4dennis/Automated-Fluid-Dispenser/AFD_SOLIDWORKS/054_BearingOuterRing_NOPRINT_N1.SLDPRT

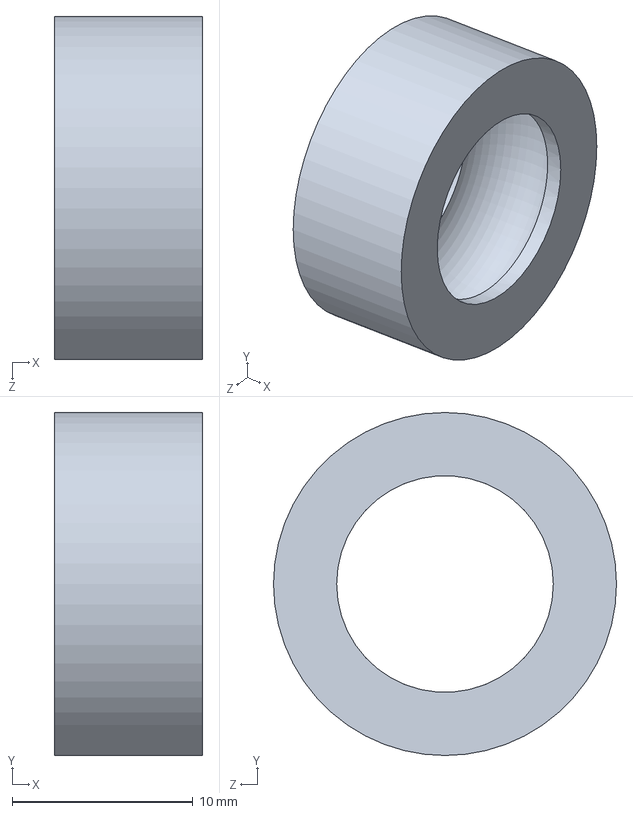
[picture p20: CAD file, 2023-12-04]
AFD_SOLIDWORKS/054_BearingOuterRing_NOPRINT_N1.SLDPRT
8.20 x 19.0 x 19.0 mm
