4dennis/Automated-Fluid-Dispenser/AFD_SOLIDWORKS/054_Motorshield_NOPRINT_N1.SLDPRT

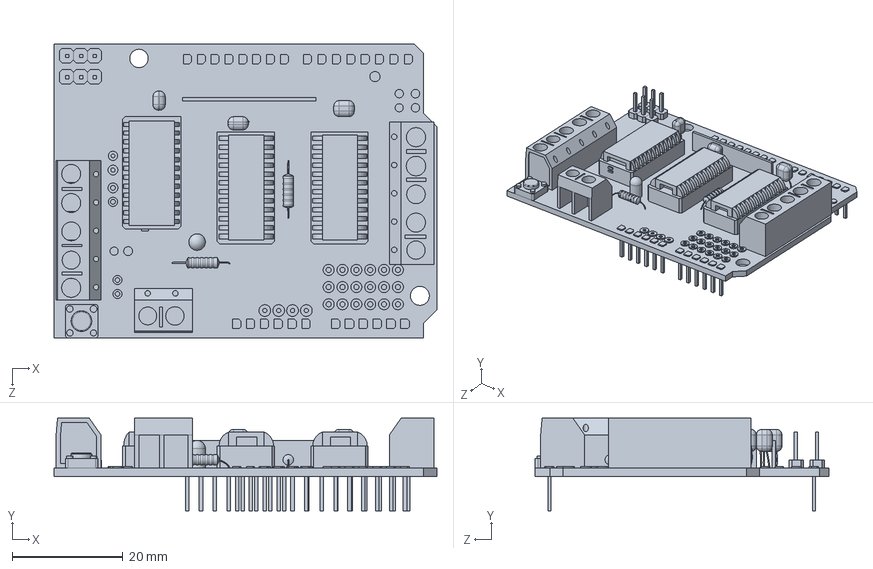
[picture p21: CAD file, 2023-12-04]
AFD_SOLIDWORKS/054_Motorshield_NOPRINT_N1.SLDPRT
69.1 x 16.7 x 53.1 mm
