4dennis/Automated-Fluid-Dispenser/AFD_SOLIDWORKS/054_Pump_NOPRINT_N1.SLDPRT

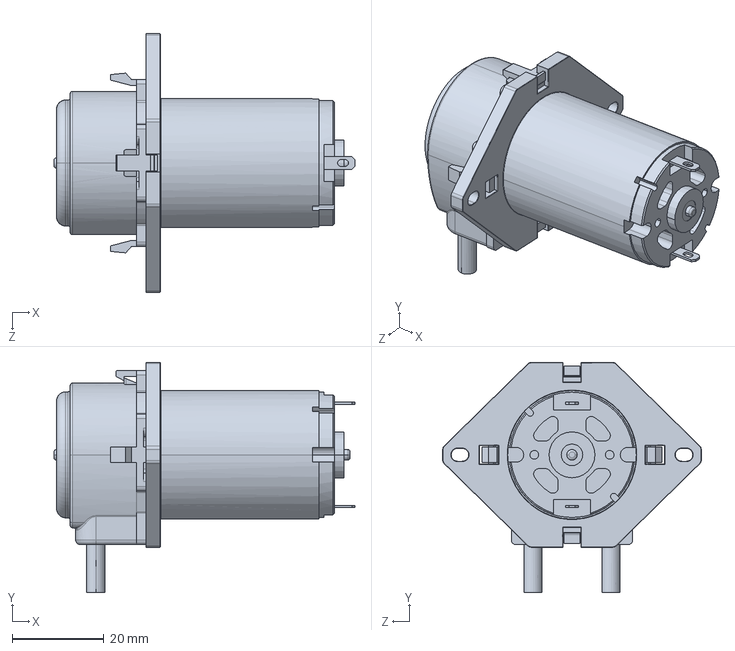
[picture p22: CAD file, 2023-12-04]
AFD_SOLIDWORKS/054_Pump_NOPRINT_N1.SLDPRT
65.5 x 50.1 x 56.3 mm
