4dennis/Automated-Fluid-Dispenser/AFD_SOLIDWORKS/054_Shaft_NOPRINT_N4.SLDPRT

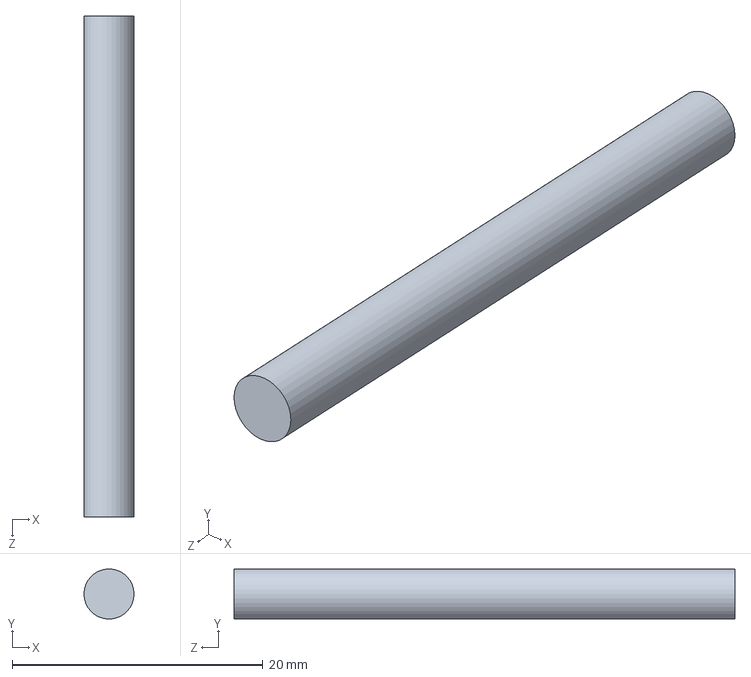
[picture p23: CAD file, 2023-12-04]
AFD_SOLIDWORKS/054_Shaft_NOPRINT_N4.SLDPRT
4.00 x 3.98 x 40.0 mm
