4dennis/Automated-Fluid-Dispenser/AFD_SOLIDWORKS/054_topofmast_AC_N1.SLDPRT

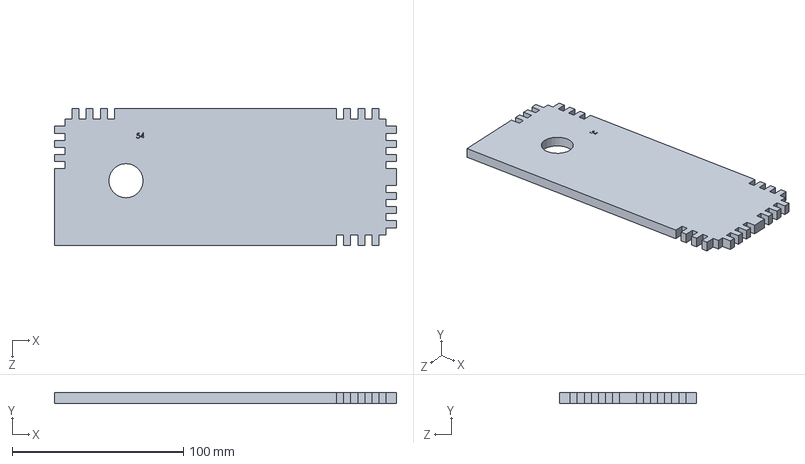
[picture p24: CAD file, 2023-12-04]
AFD_SOLIDWORKS/054_topofmast_AC_N1.SLDPRT
200.0 x 6.20 x 80.0 mm
