4dennis/Automated-Fluid-Dispenser/AFD_SOLIDWORKS/Servo_SG90 - Updated.SLDPRT

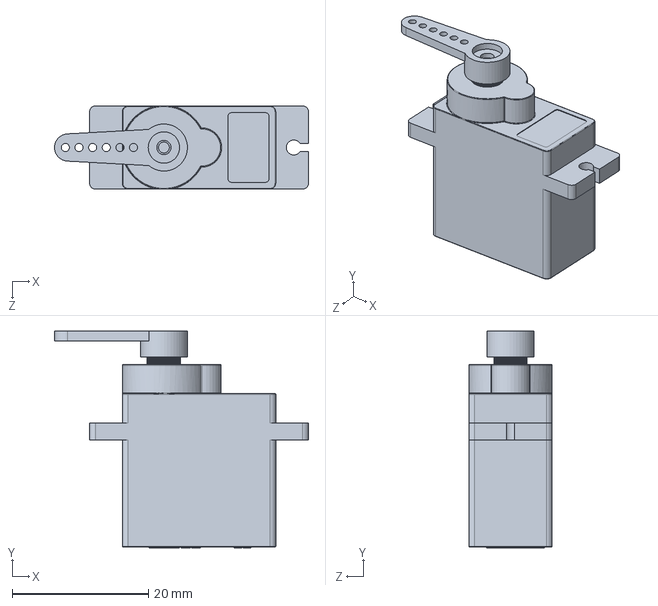
[picture p25: CAD file, 2023-12-04]
AFD_SOLIDWORKS/Servo_SG90 - Updated.SLDPRT
37.2 x 31.7 x 12.2 mm
