4dennis/Automated-Fluid-Dispenser/AFD_SOLIDWORKS/054_ArduinoHousingBottom_NOPRINT_N1.SLDPRT

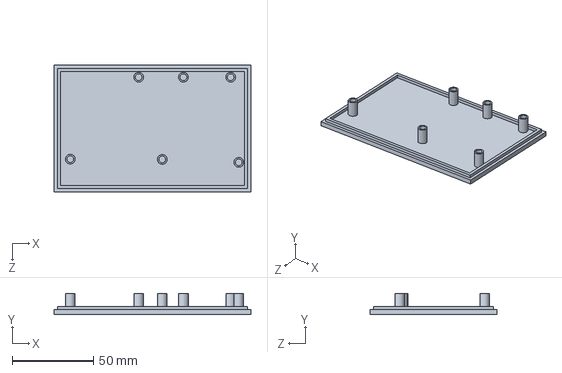
[picture p26: CAD file, 2023-12-04]
AFD_SOLIDWORKS/054_ArduinoHousingBottom_NOPRINT_N1.SLDPRT
121.0 x 13.0 x 78.0 mm
