4dennis/Automated-Fluid-Dispenser/AFD_SOLIDWORKS/054_PowderHousing_3D_N1.SLDPRT

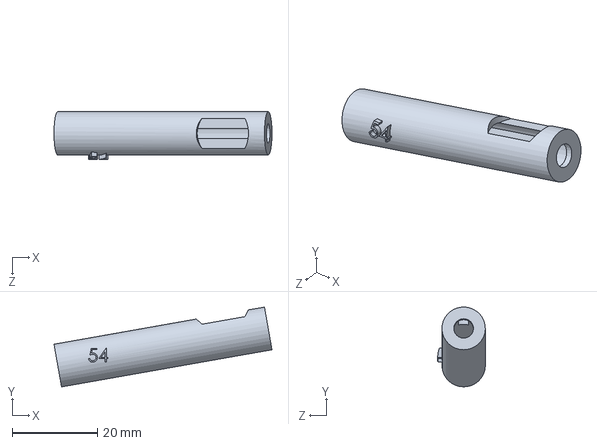
[picture p27: CAD file, 2023-12-04]
AFD_SOLIDWORKS/054_PowderHousing_3D_N1.SLDPRT
51.0 x 18.7 x 11.1 mm
