4dennis/Automated-Fluid-Dispenser/AFD_SOLIDWORKS/054_Peg_NOPRINT_N2.SLDPRT

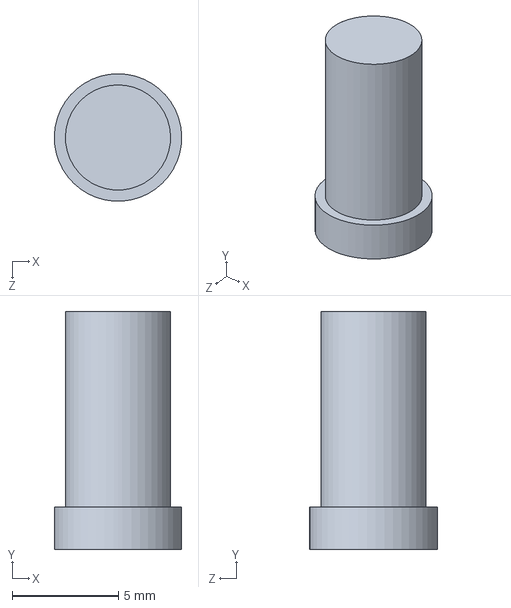
[picture p28: CAD file, 2023-12-04]
AFD_SOLIDWORKS/054_Peg_NOPRINT_N2.SLDPRT
6.00 x 11.2 x 6.00 mm
