4dennis/Automated-Fluid-Dispenser/AFD_SOLIDWORKS/054_Bushing_NOPRINT_n1.SLDPRT

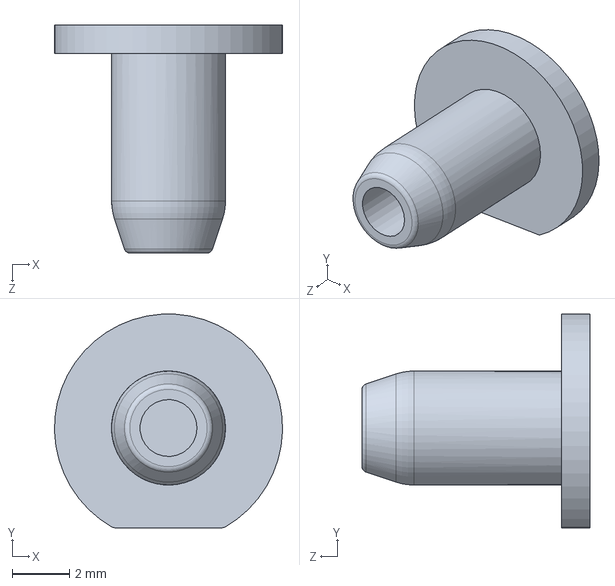
[picture p29: CAD file, 2023-12-04]
AFD_SOLIDWORKS/054_Bushing_NOPRINT_n1.SLDPRT
8.00 x 7.49 x 8.00 mm
