4dennis/Automated-Fluid-Dispenser/AFD_SOLIDWORKS/054_GearboxBack_AC_N1.SLDPRT

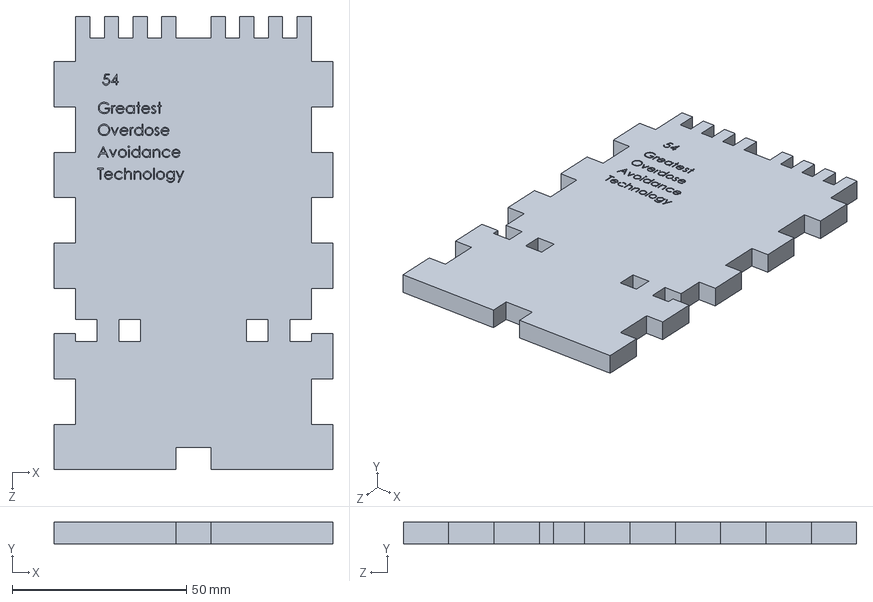
[picture p30: CAD file, 2023-12-04]
AFD_SOLIDWORKS/054_GearboxBack_AC_N1.SLDPRT
80.0 x 6.20 x 130.0 mm
