4dennis/Automated-Fluid-Dispenser/AFD_SOLIDWORKS/054_ResevoireHolder_NOPRINT_N1.SLDPRT

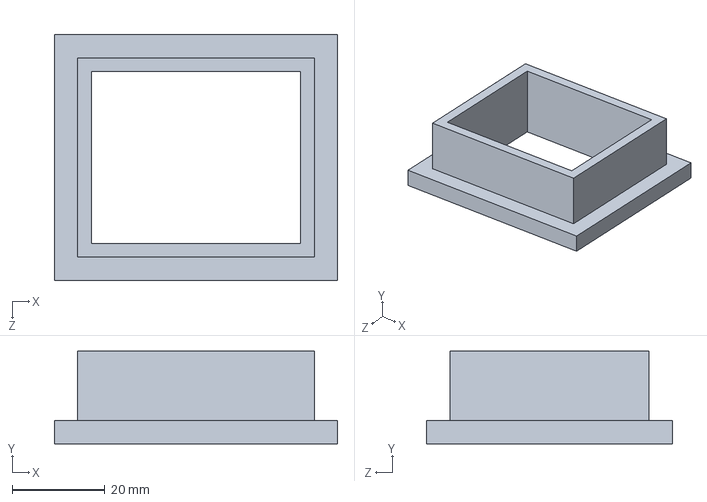
[picture p31: CAD file, 2023-12-04]
AFD_SOLIDWORKS/054_ResevoireHolder_NOPRINT_N1.SLDPRT
61.0 x 20.0 x 53.0 mm
