4dennis/Automated-Fluid-Dispenser/AFD_SOLIDWORKS/054_PowderWormDrive_3D_N1.SLDPRT

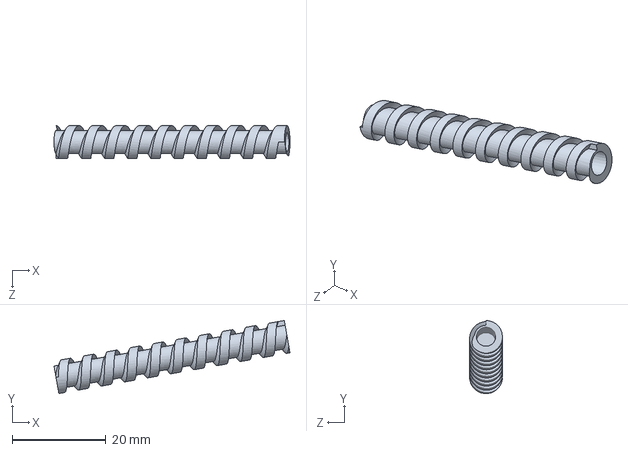
[picture p32: CAD file, 2023-12-04]
AFD_SOLIDWORKS/054_PowderWormDrive_3D_N1.SLDPRT
50.3 x 15.6 x 7.00 mm
