4dennis/Automated-Fluid-Dispenser/AFD_SOLIDWORKS/054_GearboxBottom1_AC_N1.SLDPRT

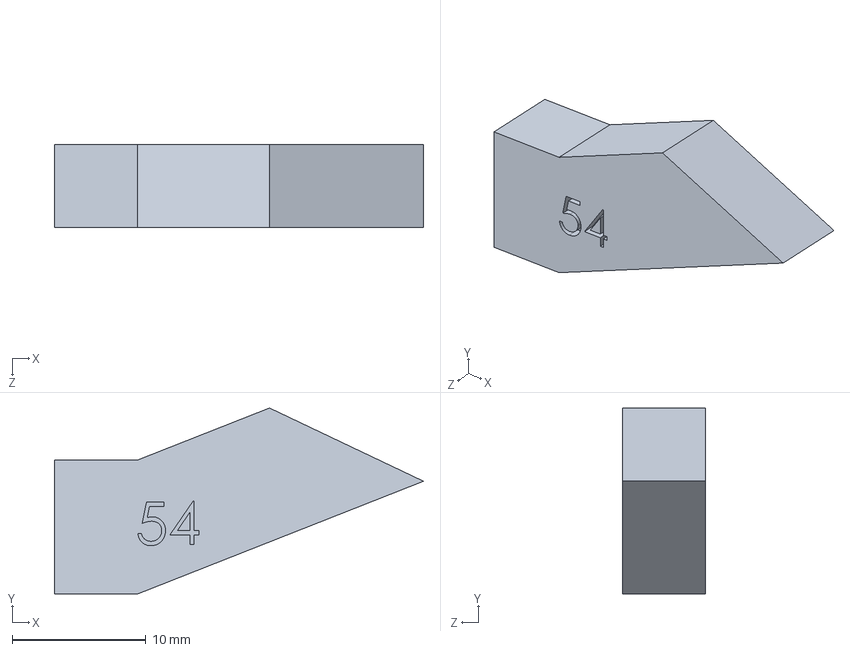
[picture p33: CAD file, 2023-12-04]
AFD_SOLIDWORKS/054_GearboxBottom1_AC_N1.SLDPRT
27.5 x 13.9 x 6.20 mm
