4dennis/Automated-Fluid-Dispenser/AFD_SOLIDWORKS/054_NewPowderFunnel_3D_N1.SLDPRT

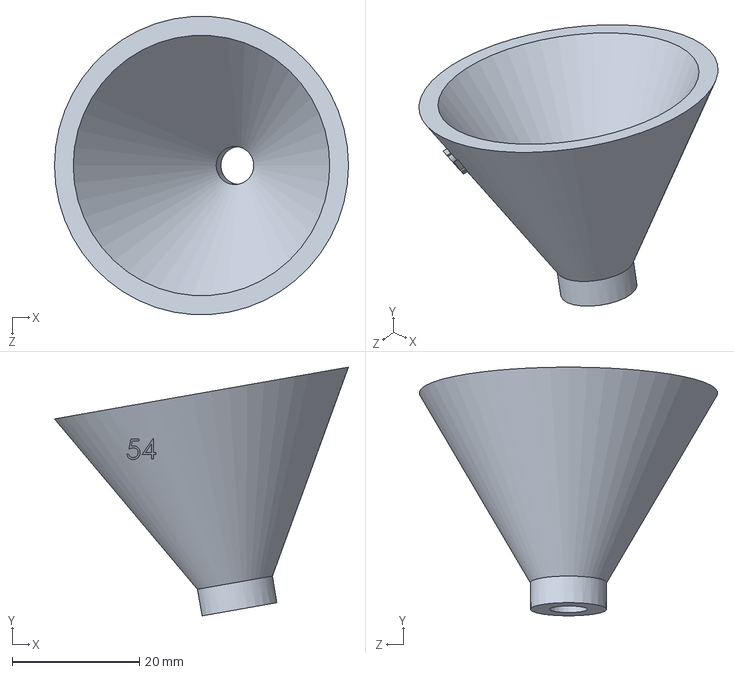
[picture p34: CAD file, 2023-12-04]
AFD_SOLIDWORKS/054_NewPowderFunnel_3D_N1.SLDPRT
46.3 x 39.2 x 46.9 mm
