4dennis/Automated-Fluid-Dispenser/AFD_SOLIDWORKS/DCMotor1.SLDPRT

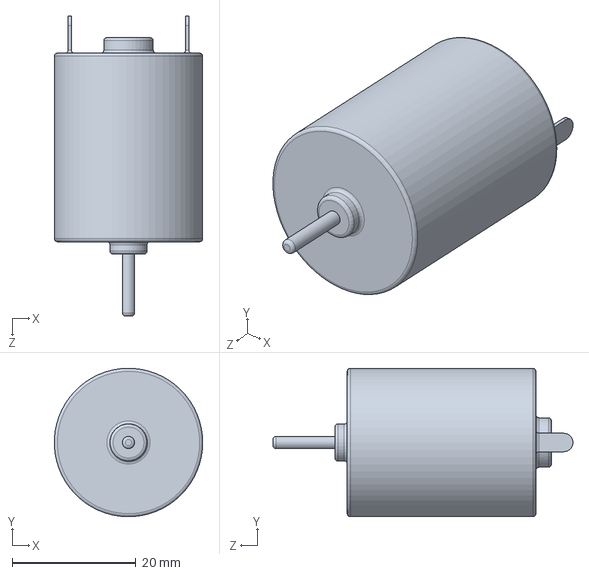
[picture p35: CAD file, 2023-12-04]
AFD_SOLIDWORKS/DCMotor1.SLDPRT
24.0 x 24.0 x 48.5 mm
