4dennis/Automated-Fluid-Dispenser/AFD_SOLIDWORKS/054_PowderStand_NOPRINT_N1.SLDPRT

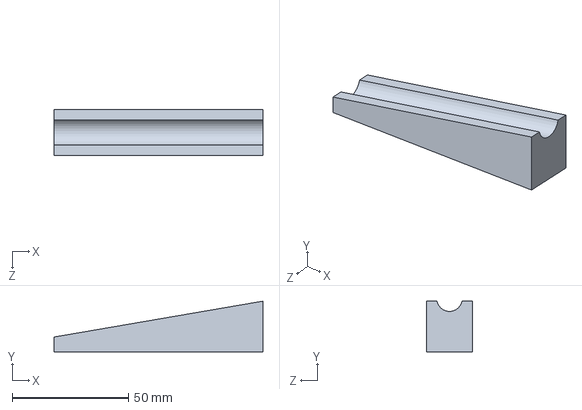
[picture p36: CAD file, 2023-12-04]
AFD_SOLIDWORKS/054_PowderStand_NOPRINT_N1.SLDPRT
90.0 x 21.8 x 20.0 mm
