4dennis/Automated-Fluid-Dispenser/AFD_SOLIDWORKS/054_TestTube_NOPRINT_N5.SLDPRT

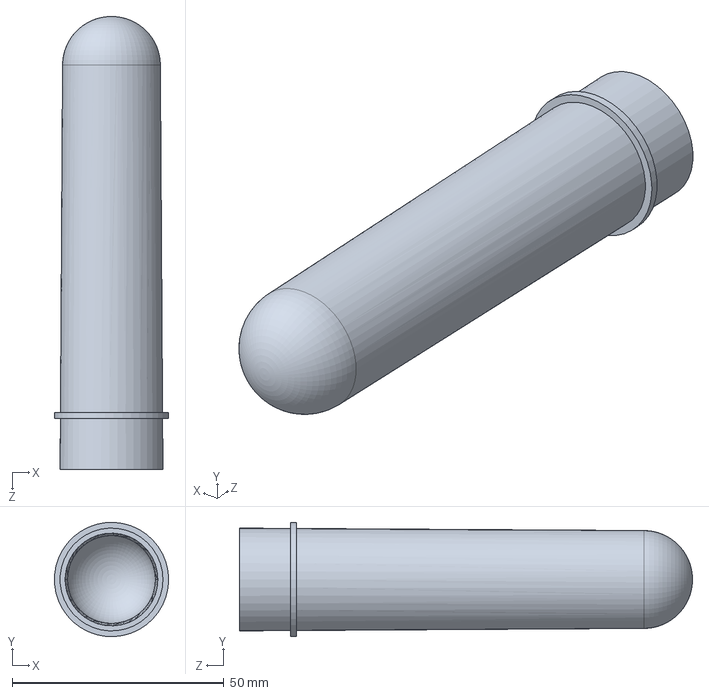
[picture p37: CAD file, 2023-12-04]
AFD_SOLIDWORKS/054_TestTube_NOPRINT_N5.SLDPRT
27.0 x 27.0 x 107.0 mm
