4dennis/Automated-Fluid-Dispenser/AFD_SOLIDWORKS/054_GearboxBottom4_AC_N1.SLDPRT

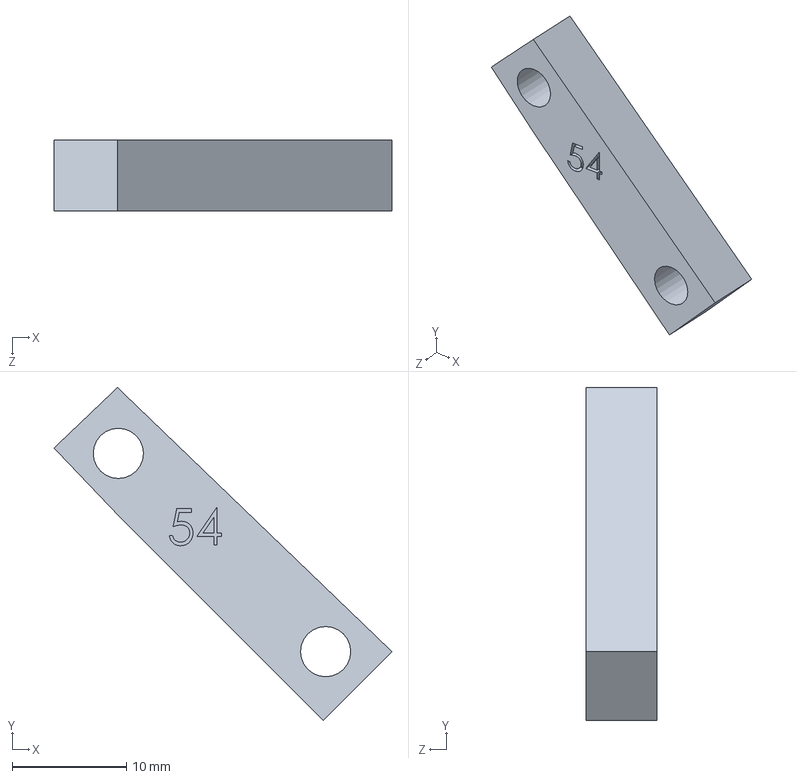
[picture p38: CAD file, 2023-12-04]
AFD_SOLIDWORKS/054_GearboxBottom4_AC_N1.SLDPRT
29.6 x 29.2 x 6.20 mm
