4dennis/Automated-Fluid-Dispenser/AFD_SOLIDWORKS/054_40T_NOPRINT_N2.SLDPRT

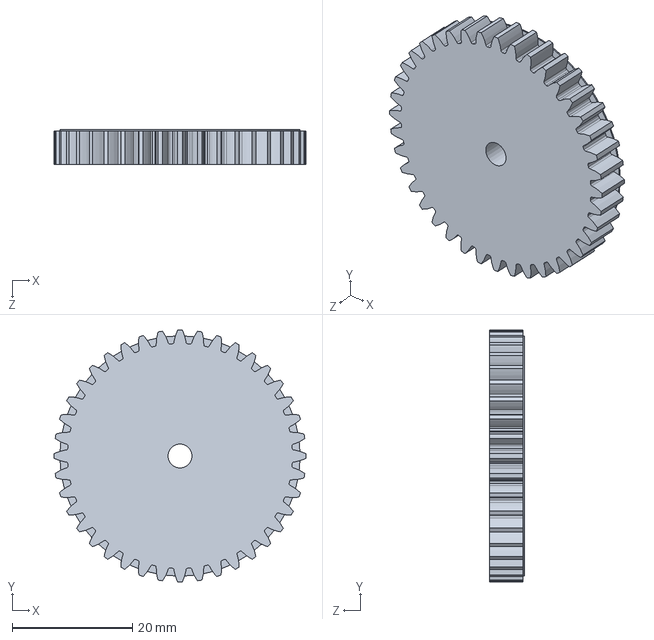
[picture p39: CAD file, 2023-12-04]
AFD_SOLIDWORKS/054_40T_NOPRINT_N2.SLDPRT
42.0 x 42.0 x 5.85 mm
