4dennis/Automated-Fluid-Dispenser/AFD_SOLIDWORKS/054_GearboxBottom2_AC_N1.SLDPRT

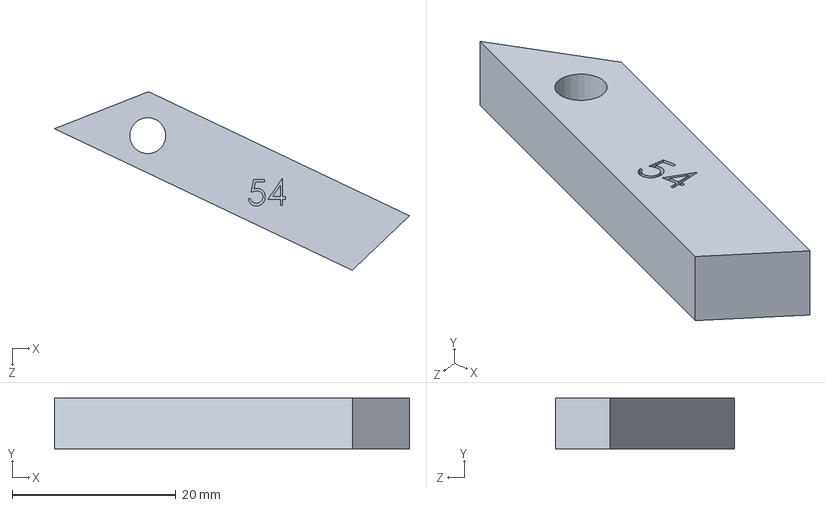
[picture p40: CAD file, 2023-12-04]
AFD_SOLIDWORKS/054_GearboxBottom2_AC_N1.SLDPRT
43.4 x 6.20 x 21.8 mm
