4dennis/Automated-Fluid-Dispenser/AFD_SOLIDWORKS/054_Pegboard_NOPRINT_N1.SLDPRT

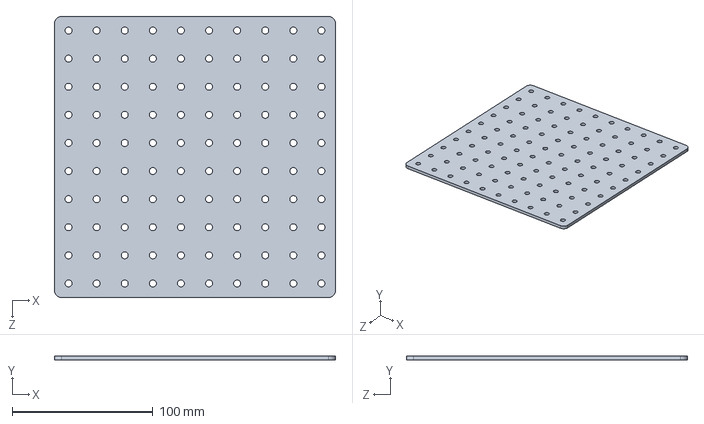
[picture p41: CAD file, 2023-12-04]
AFD_SOLIDWORKS/054_Pegboard_NOPRINT_N1.SLDPRT
200.0 x 3.00 x 200.0 mm
