4dennis/Automated-Fluid-Dispenser/AFD_SOLIDWORKS/054_LimitSwitch_NOPRINT_N1.SLDPRT

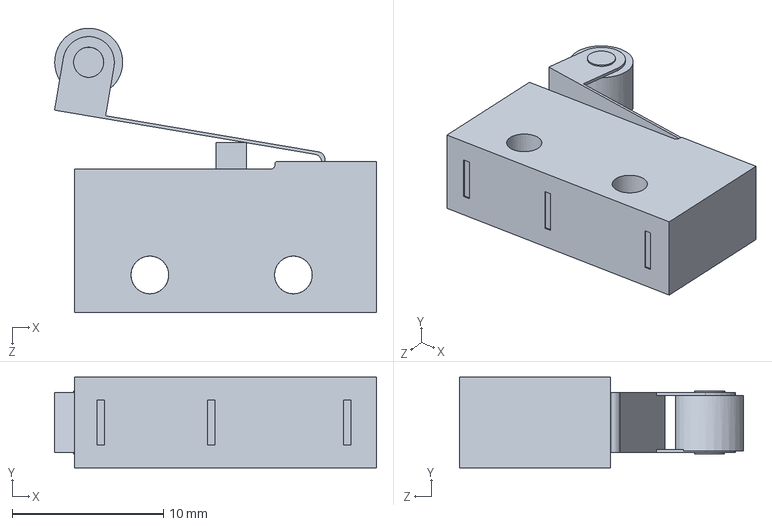
[picture p42: CAD file, 2023-12-04]
AFD_SOLIDWORKS/054_LimitSwitch_NOPRINT_N1.SLDPRT
21.3 x 6.00 x 18.8 mm
