4dennis/Automated-Fluid-Dispenser/AFD_SOLIDWORKS/054_Reservoir_NOPRINT_N1.SLDPRT

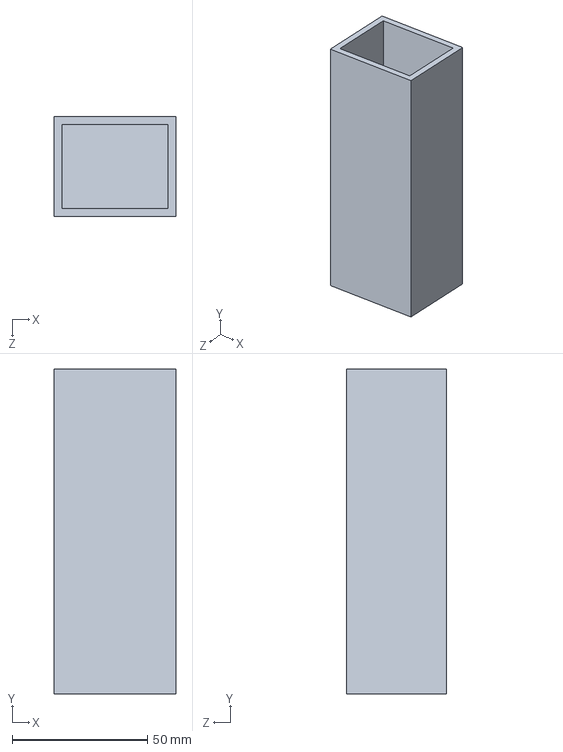
[picture p43: CAD file, 2023-12-04]
AFD_SOLIDWORKS/054_Reservoir_NOPRINT_N1.SLDPRT
45.0 x 120.0 x 37.0 mm
