4dennis/Automated-Fluid-Dispenser/AFD_SOLIDWORKS/054_30T_NOPRINT_N1.SLDPRT

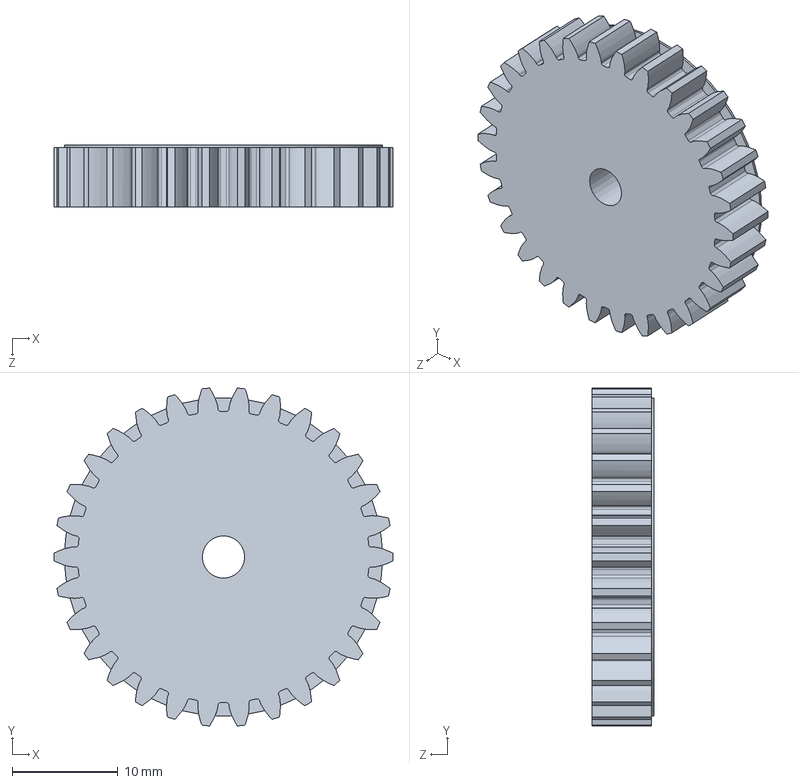
[picture p44: CAD file, 2023-12-04]
AFD_SOLIDWORKS/054_30T_NOPRINT_N1.SLDPRT
32.0 x 31.9 x 5.85 mm
