4dennis/Automated-Fluid-Dispenser/AFD_SOLIDWORKS/054_ArduinoUno_NOPRINT_N1.SLDPRT

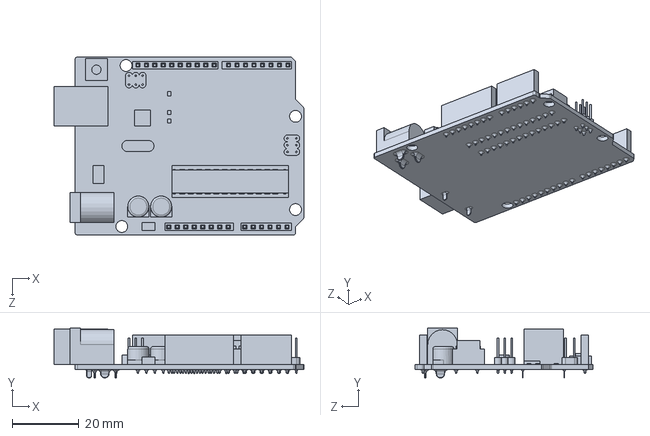
[picture p45: CAD file, 2023-12-04]
AFD_SOLIDWORKS/054_ArduinoUno_NOPRINT_N1.SLDPRT
74.9 x 15.0 x 53.3 mm
