4dennis/Automated-Fluid-Dispenser/AFD_SOLIDWORKS/054_GearboxBottom3_AC_N1.SLDPRT

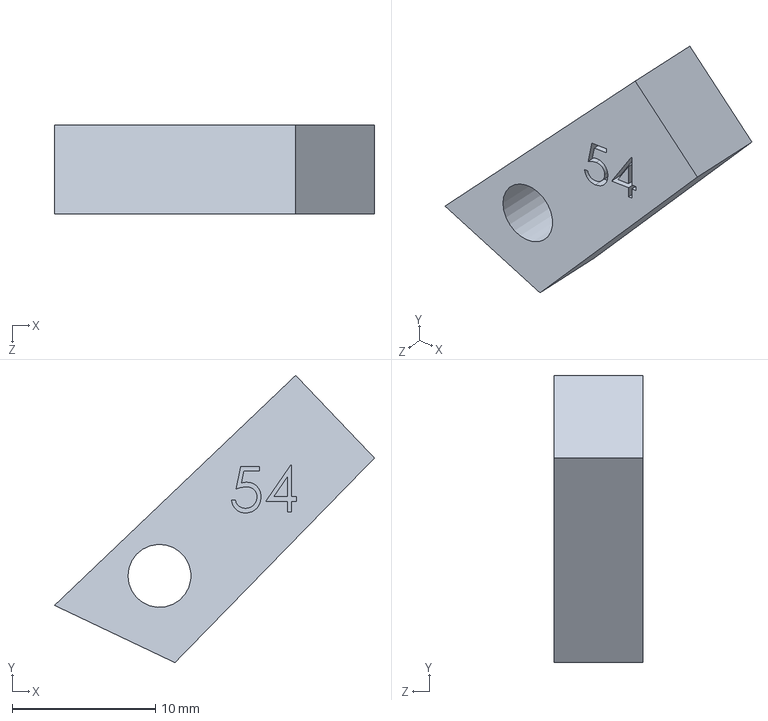
[picture p46: CAD file, 2023-12-04]
AFD_SOLIDWORKS/054_GearboxBottom3_AC_N1.SLDPRT
22.4 x 20.1 x 6.20 mm
