4dennis/Automated-Fluid-Dispenser/AFD_SOLIDWORKS/054_GearboxSide2_AC_N1.SLDPRT

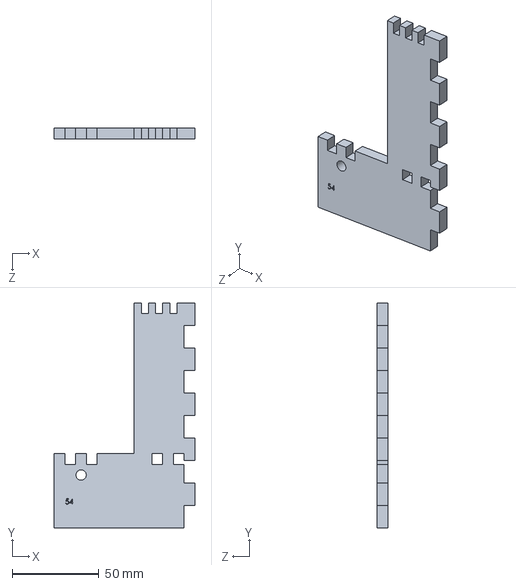
[picture p47: CAD file, 2023-12-04]
AFD_SOLIDWORKS/054_GearboxSide2_AC_N1.SLDPRT
81.3 x 130.0 x 6.20 mm
